freeDSP/FreeDSP_Catamaran_AB/Optinal Balanced Driver Board/Photos/BalancedDriverBoard.jpg

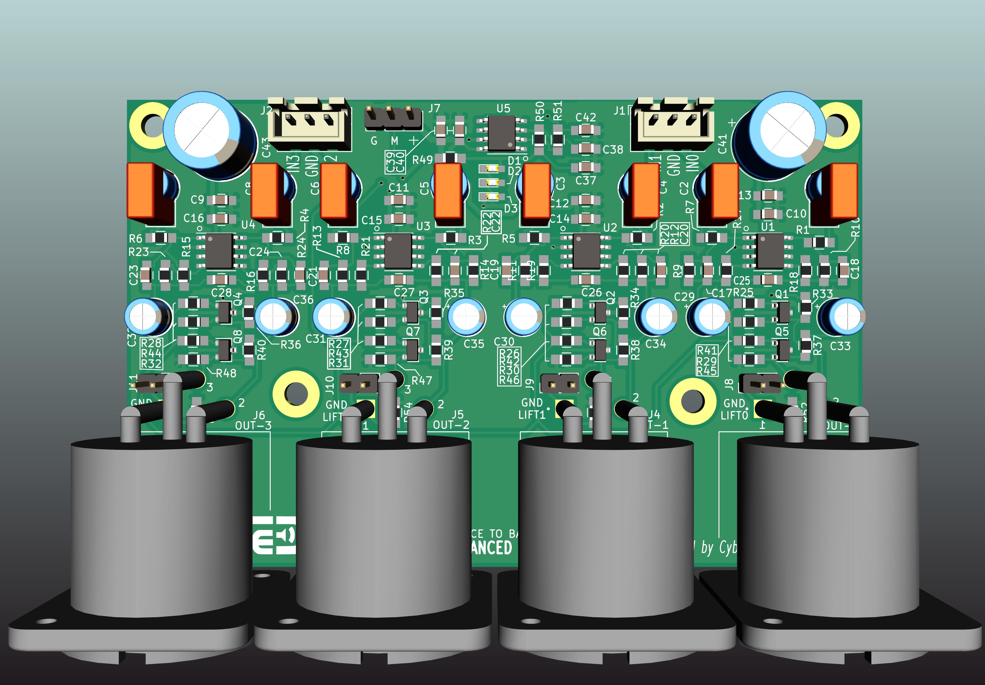
Optinal Balanced Driver Board/Photos/BalancedDriverBoard.jpg
