freeDSP/FreeDSP_Catamaran_AB/Optinal Balanced Driver Board/Photos/BalancedDriverBoard_Bottom.jpg

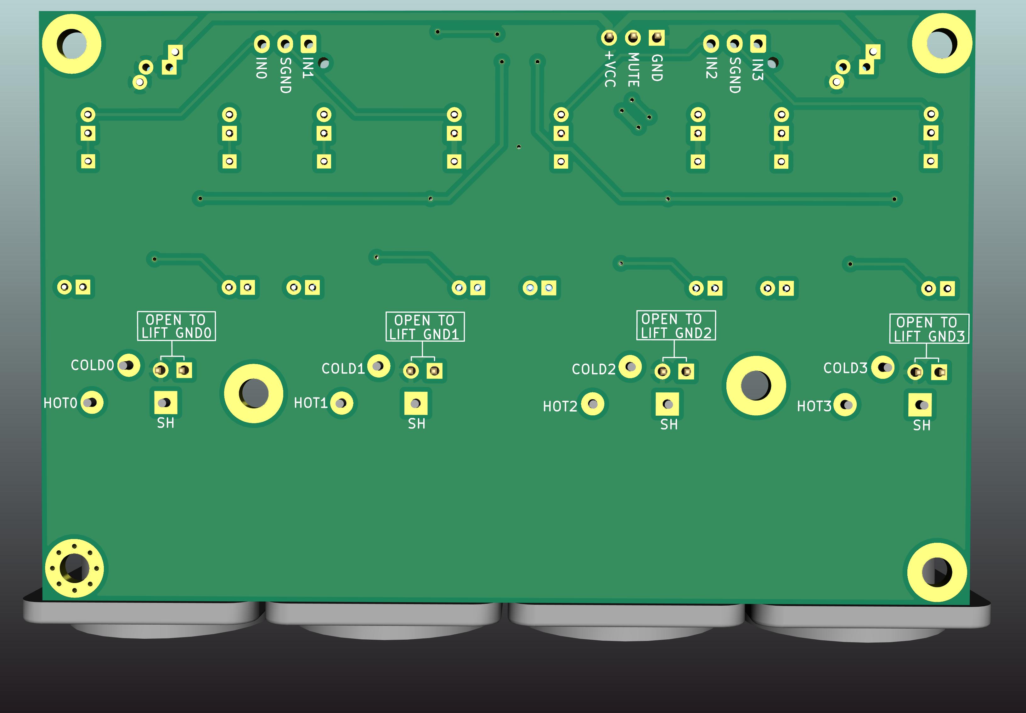
Optinal Balanced Driver Board/Photos/BalancedDriverBoard_Bottom.jpg
