freeDSP/FreeDSP_Catamaran_AB/Optinal Balanced Driver Board/Photos/BalancedDriverBoard_BottomRayTrace.jpg

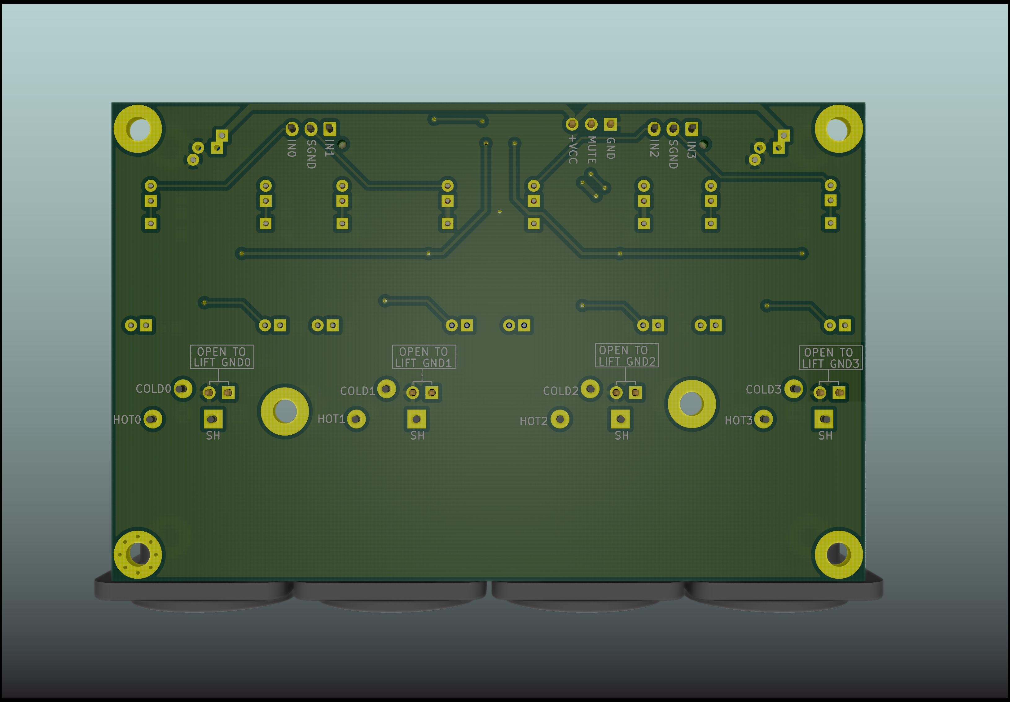
Optinal Balanced Driver Board/Photos/BalancedDriverBoard_BottomRayTrace.jpg
