freeDSP/FreeDSP_Catamaran_AB/Optinal Balanced Driver Board/Photos/BalancedDriverBoard_RayTrace.jpg

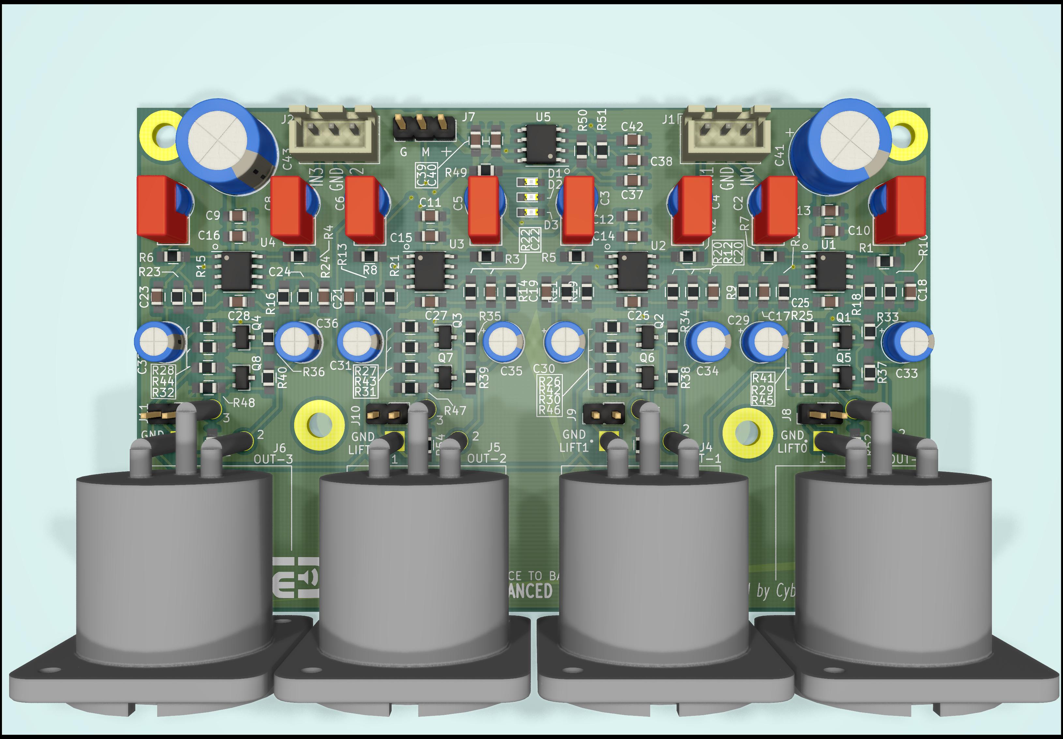
Optinal Balanced Driver Board/Photos/BalancedDriverBoard_RayTrace.jpg
