freeDSP/FreeDSP_Catamaran_AB/Optinal Balanced Driver Board/Photos/BalancedDriverBoardImage.jpg

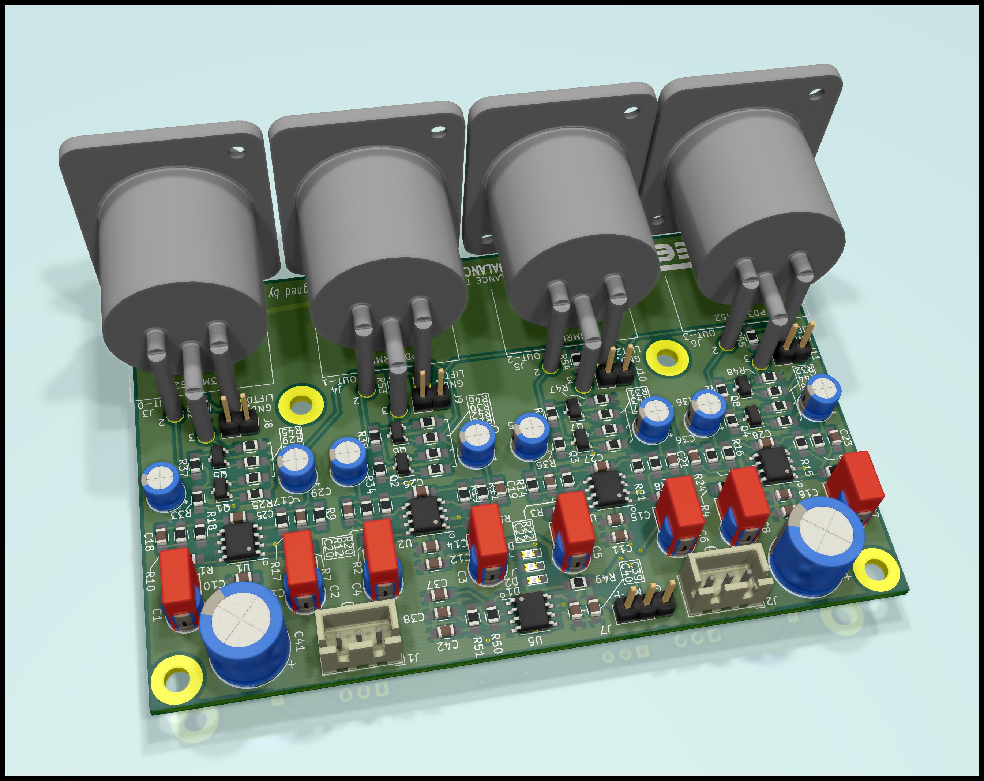
Optinal Balanced Driver Board/Photos/BalancedDriverBoardImage.jpg
