freeDSP/FreeDSP_Catamaran_AB/Photo/0v21PaseView copy.jpg

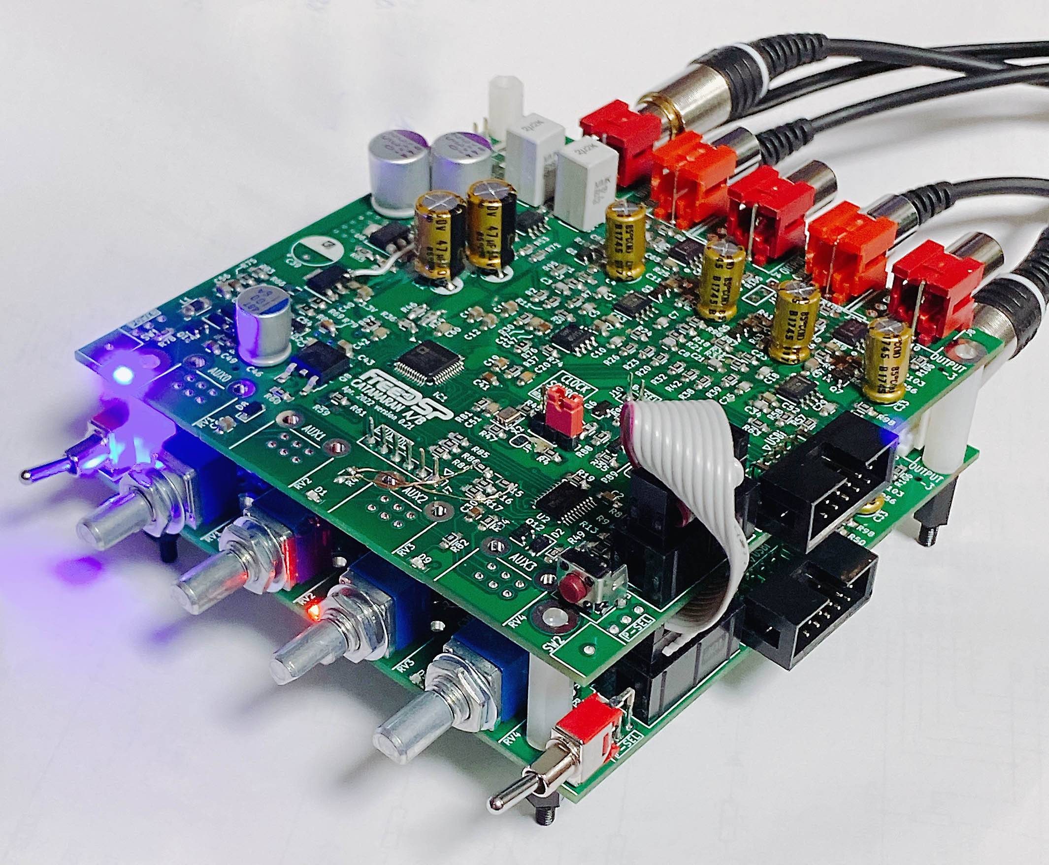
Photo/0v21PaseView copy.jpg
