freeDSP/FreeDSP_Catamaran_AB/Photo/1kHzCrosstalk.png

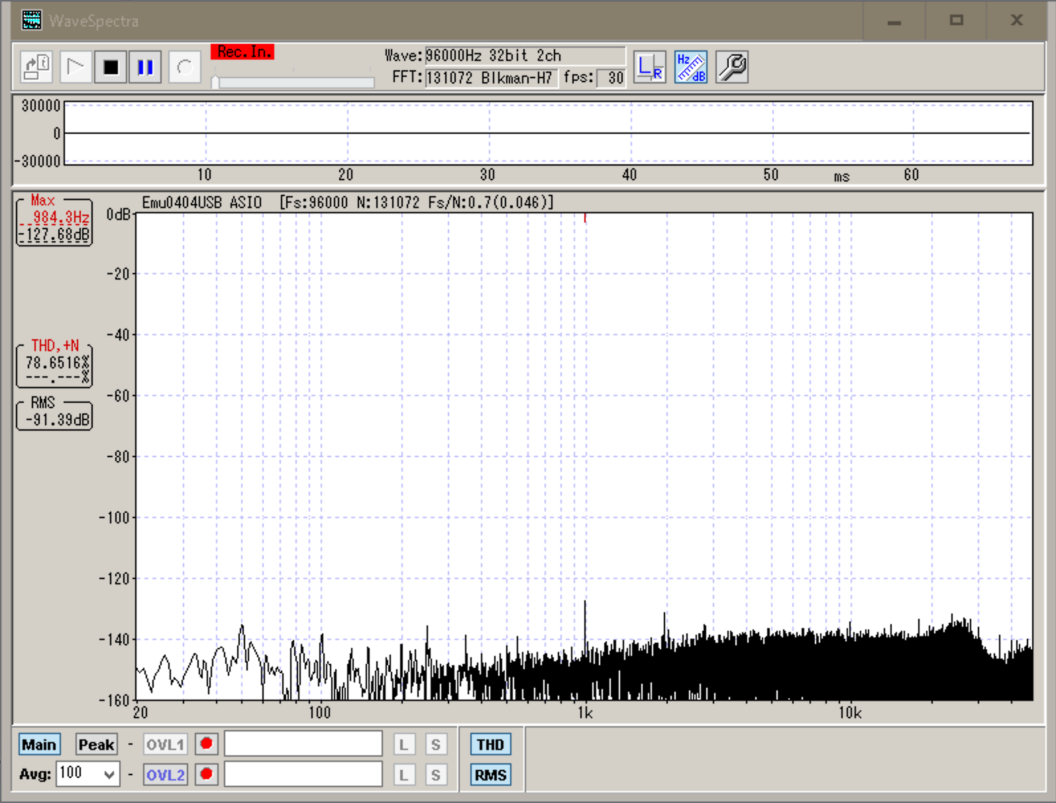
Photo/1kHzCrosstalk.png
