freeDSP/FreeDSP_Catamaran_AB/Photo/4wayCroosover48dBOct.gif

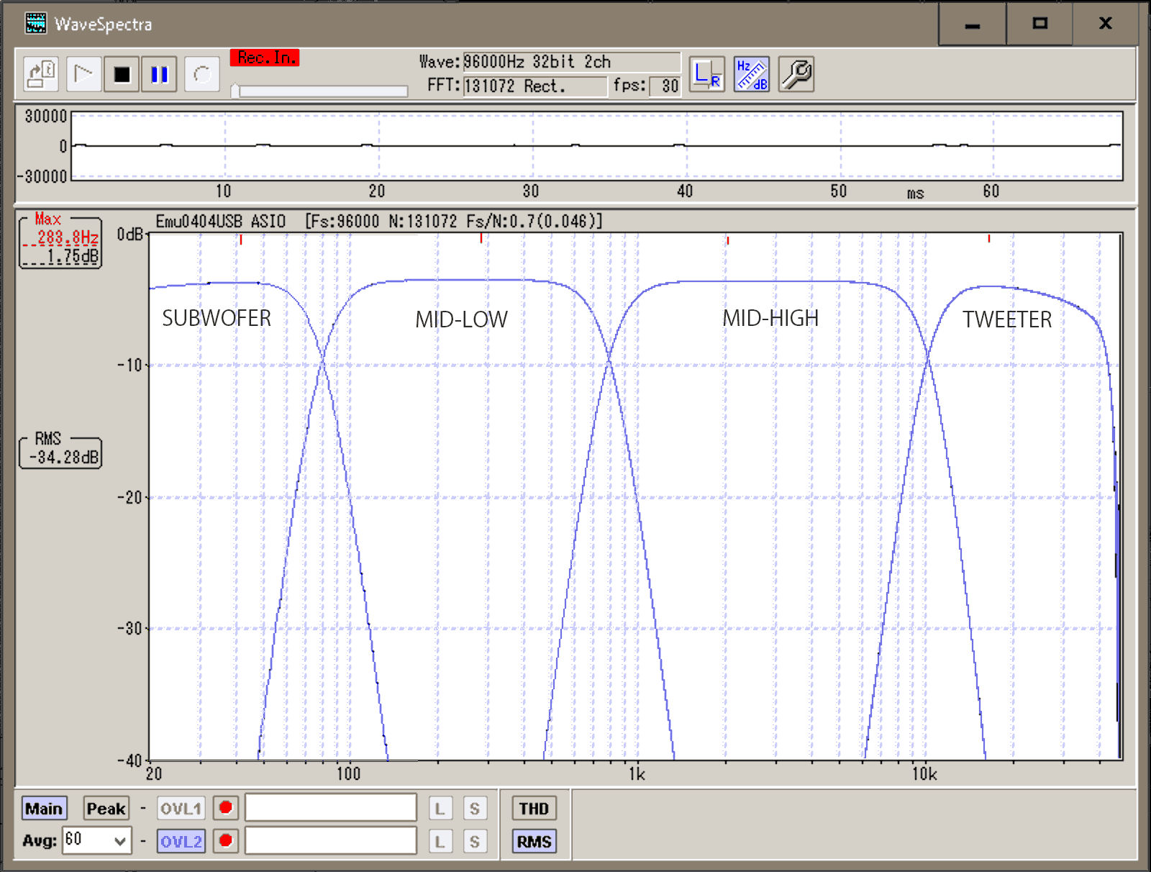
Photo/4wayCroosover48dBOct.gif
