freeDSP/FreeDSP_Catamaran_AB/Photo/FreeDSP_Caramaran_0v21_Master_Photo.JPG

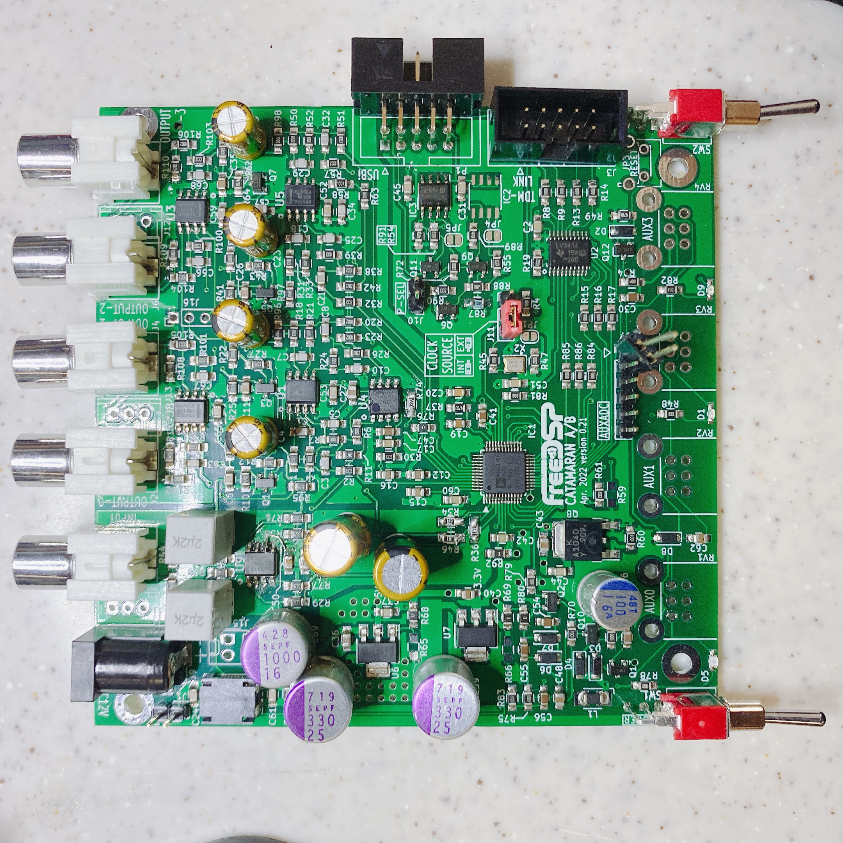
Photo/FreeDSP_Caramaran_0v21_Master_Photo.JPG
