freeDSP/FreeDSP_Catamaran_AB/Photo/FreeDSP_Caramaran_0v21_Slave_Photo.JPG

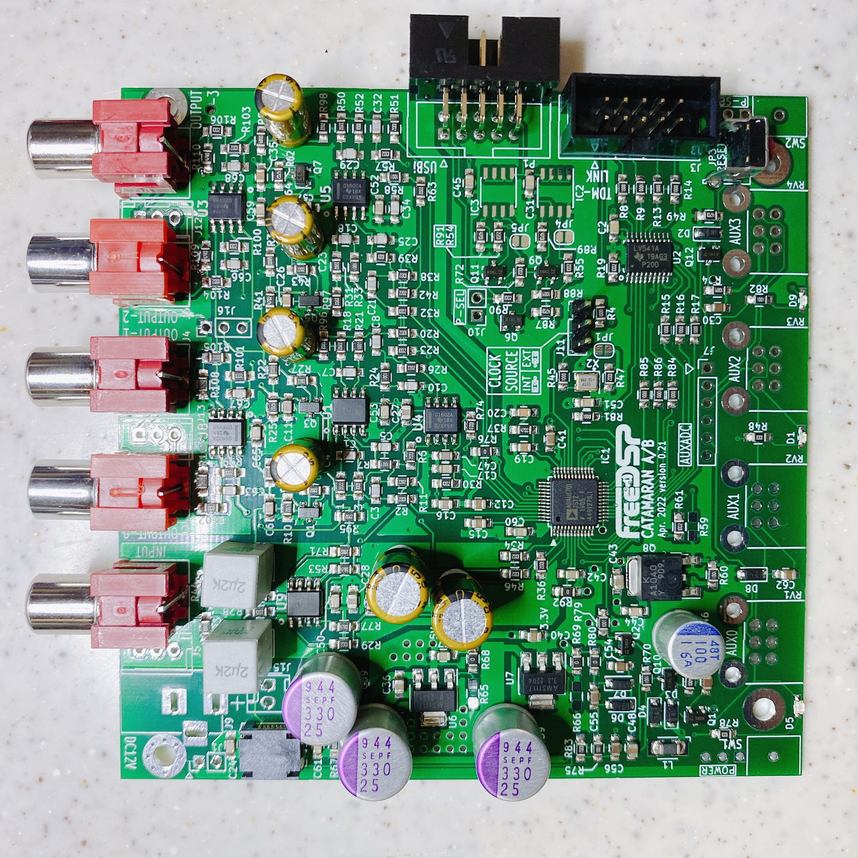
Photo/FreeDSP_Caramaran_0v21_Slave_Photo.JPG
