freeDSP/FreeDSP_Catamaran_AB/Photo/FreeDSP_Catamaran0v2.jpg

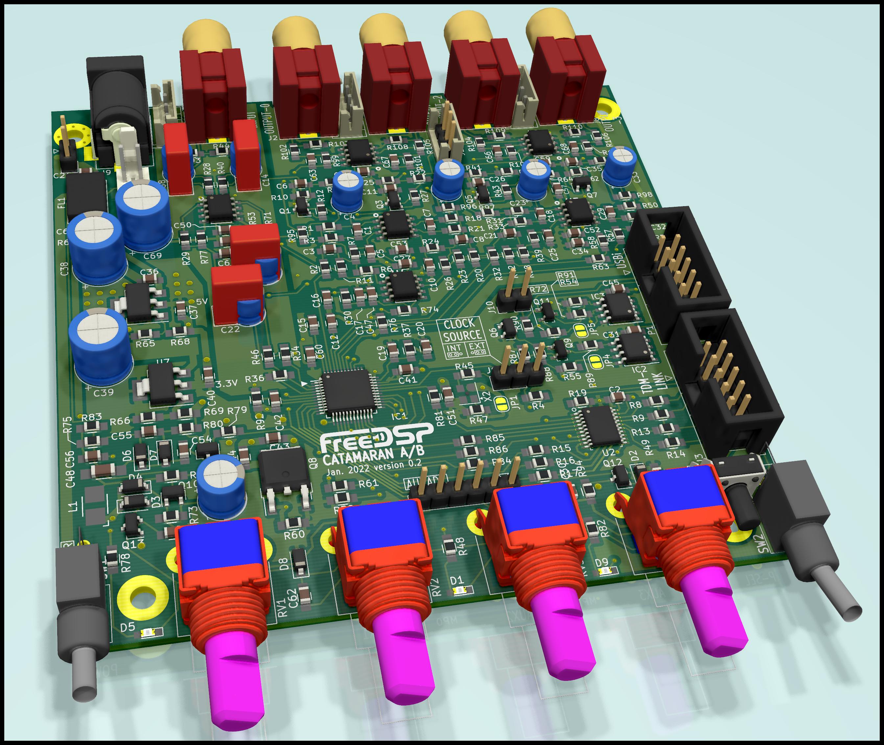
Photo/FreeDSP_Catamaran0v2.jpg
