freeDSP/FreeDSP_Catamaran_AB/Photo/FreeDSP_Catamaran0v2BottomView.jpg

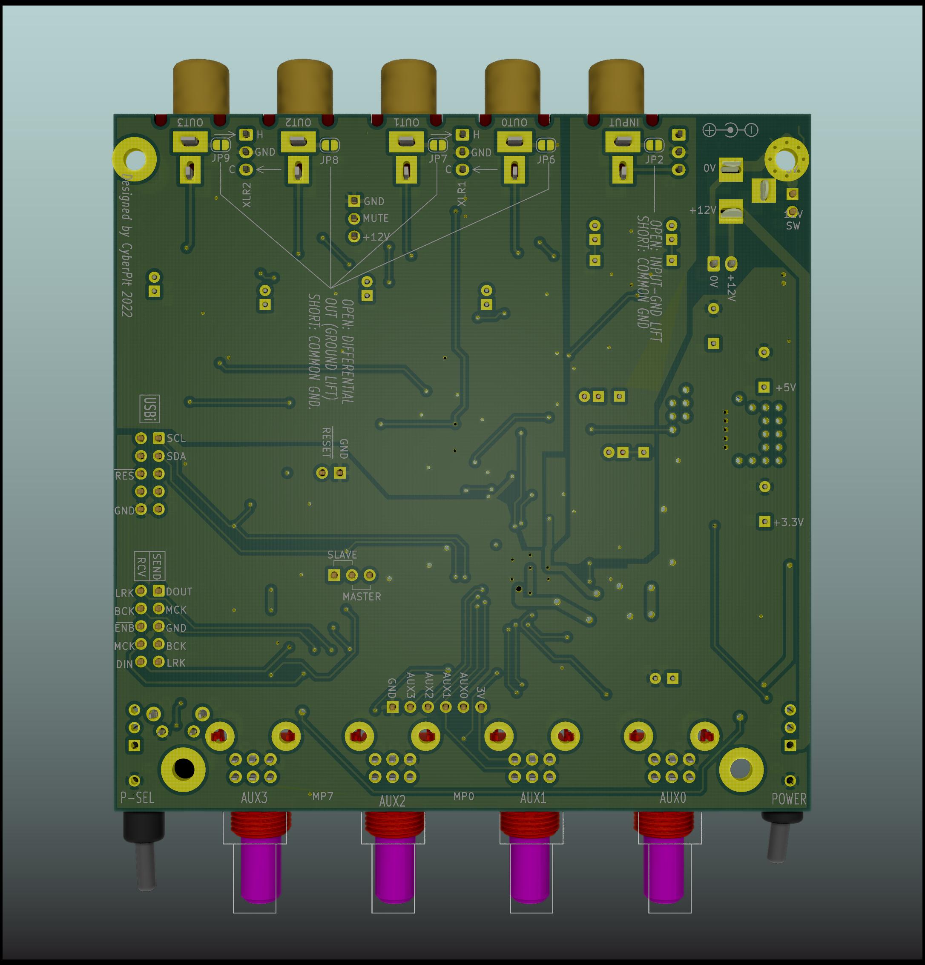
Photo/FreeDSP_Catamaran0v2BottomView.jpg
