freeDSP/FreeDSP_Catamaran_AB/Photo/FreeDSP_Catamaran0v2TopView.jpg

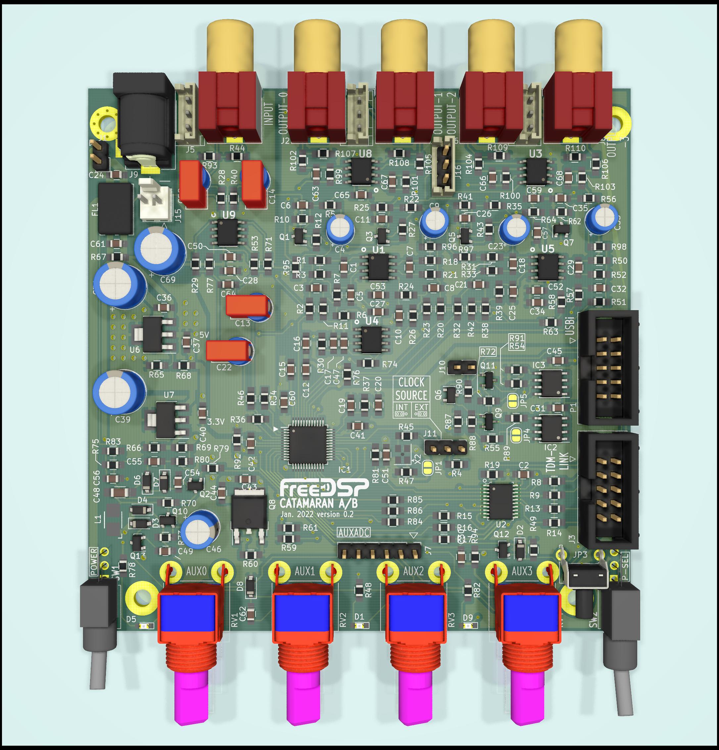
Photo/FreeDSP_Catamaran0v2TopView.jpg
