freeDSP/FreeDSP_Catamaran_AB/Photo/FreeDSP_Catamaran_1v0_TopRender.jpg

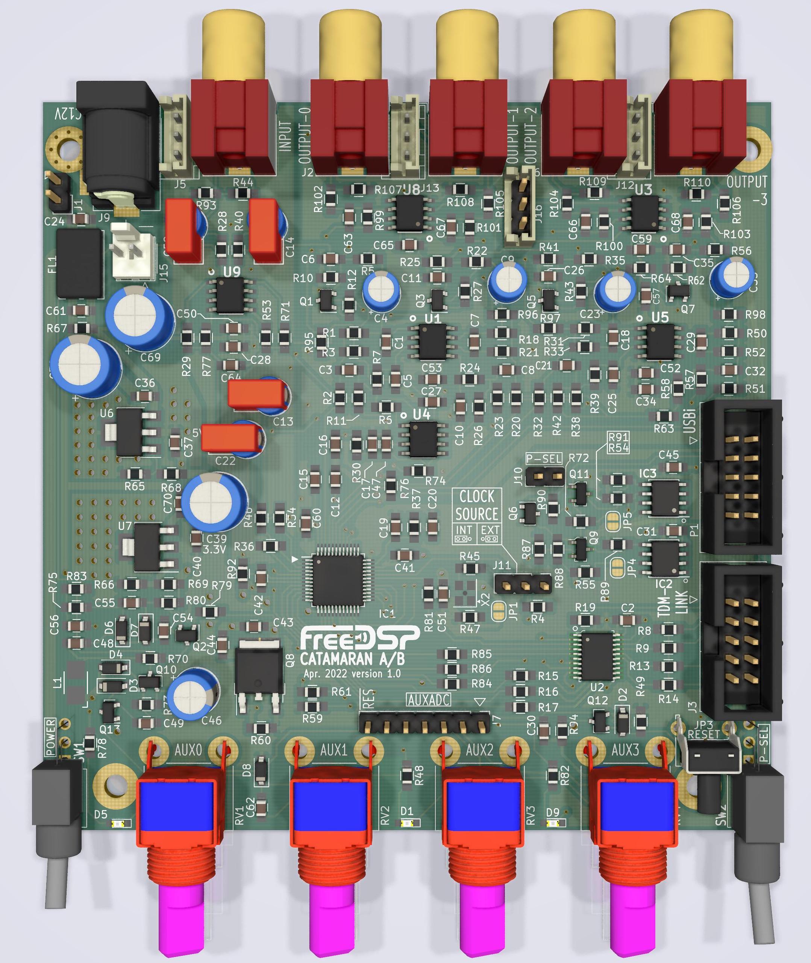
Photo/FreeDSP_Catamaran_1v0_TopRender.jpg
