freeDSP/FreeDSP_Catamaran_AB/Photo/FreeDSP_Catamaran_1v2_TopRendering.jpg

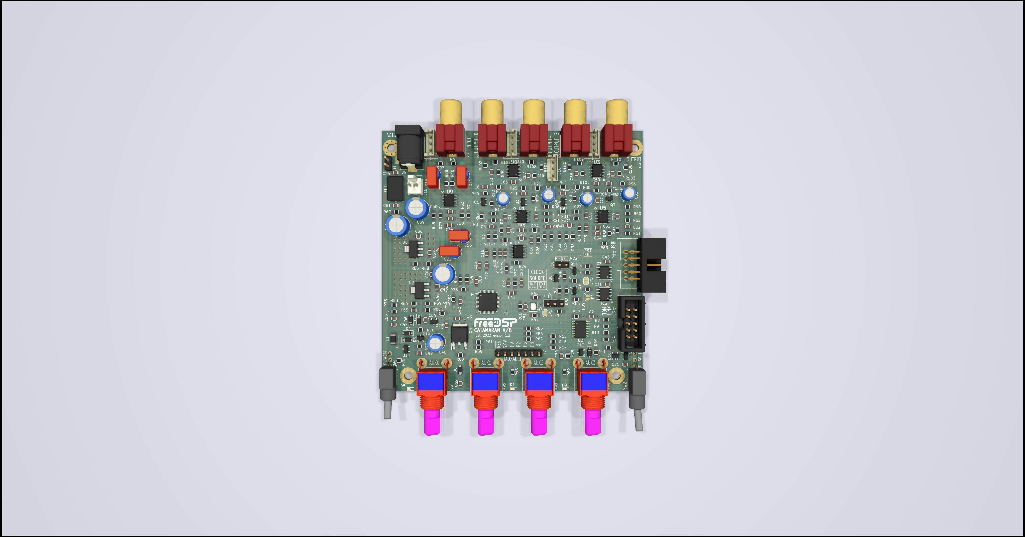
Photo/FreeDSP_Catamaran_1v2_TopRendering.jpg
