freeDSP/FreeDSP_Catamaran_AB/Photo/FreeDSP_Catamaran_SinWave96kHzOverallDistortion.png

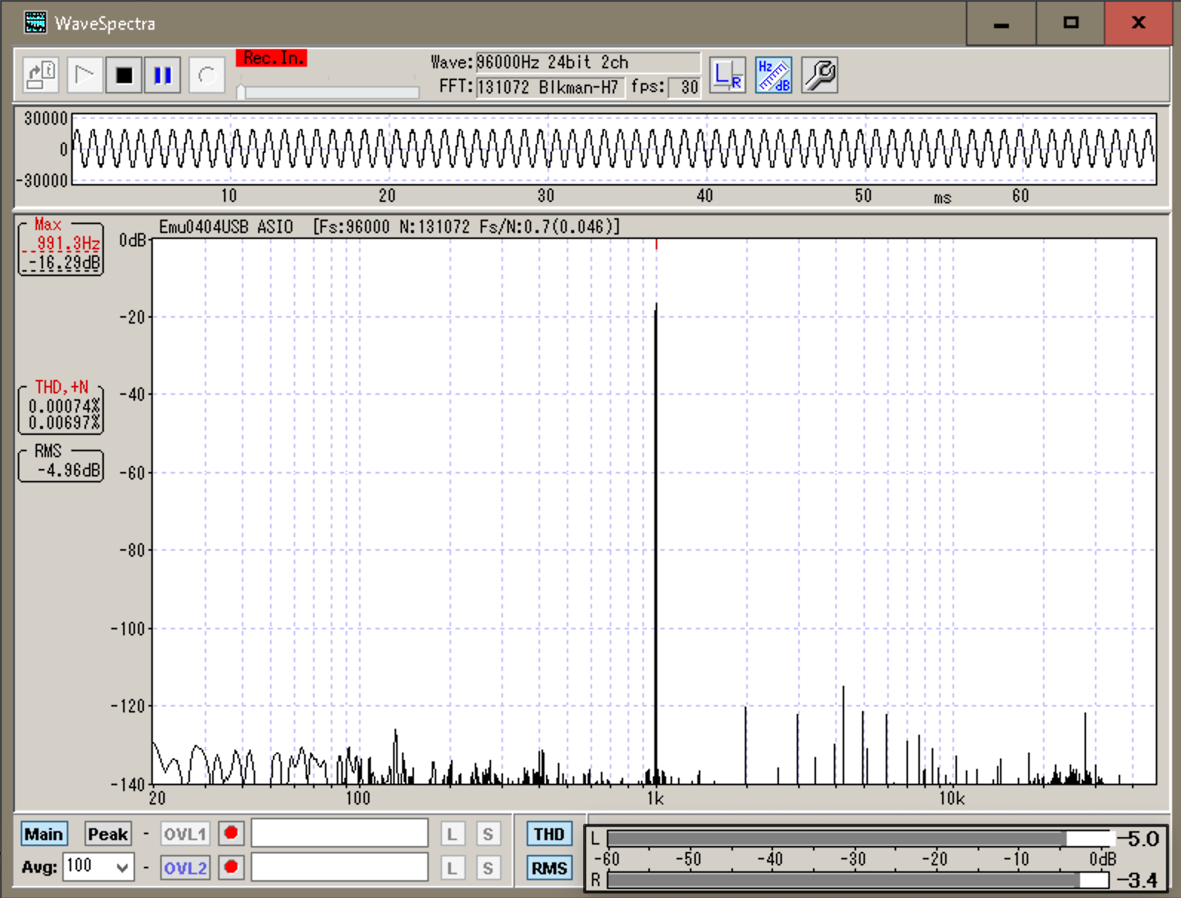
Photo/FreeDSP_Catamaran_SinWave96kHzOverallDistortion.png
