freeDSP/FreeDSP_Catamaran_AB/Photo/IMG_5258.JPG

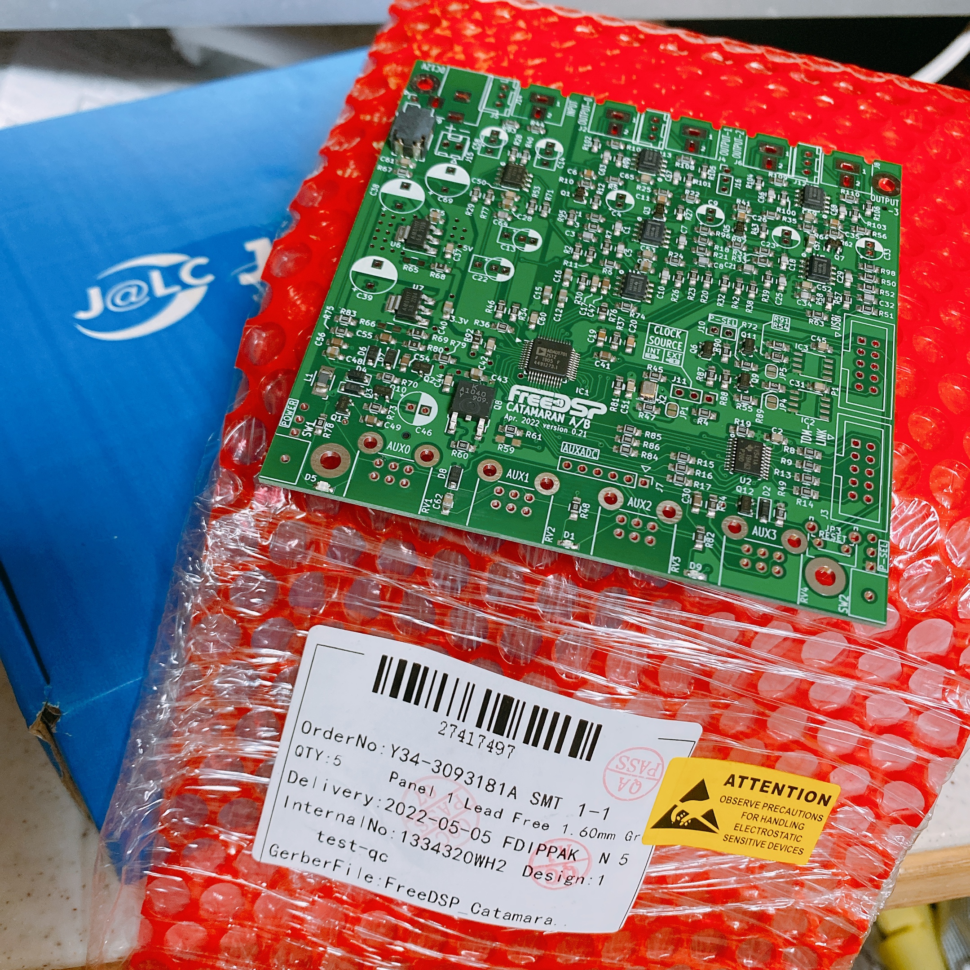
Photo/IMG_5258.JPG
