freeDSP/FreeDSP_Catamaran_AB/Photo/MainBoard_Bottom.JPG

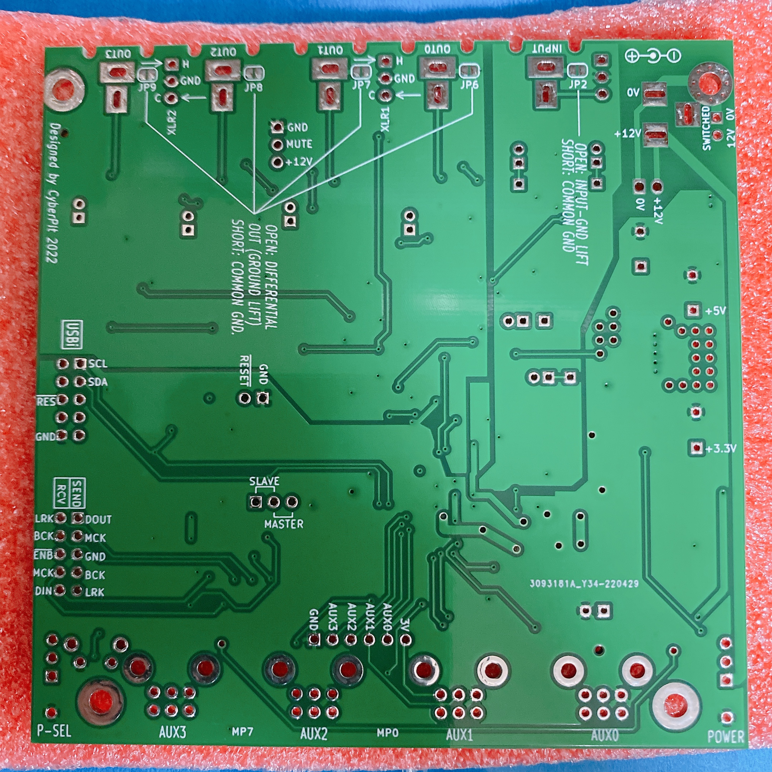
Photo/MainBoard_Bottom.JPG
