freeDSP/FreeDSP_Catamaran_AB/Photo/MainBoard_Top-SMT.JPG

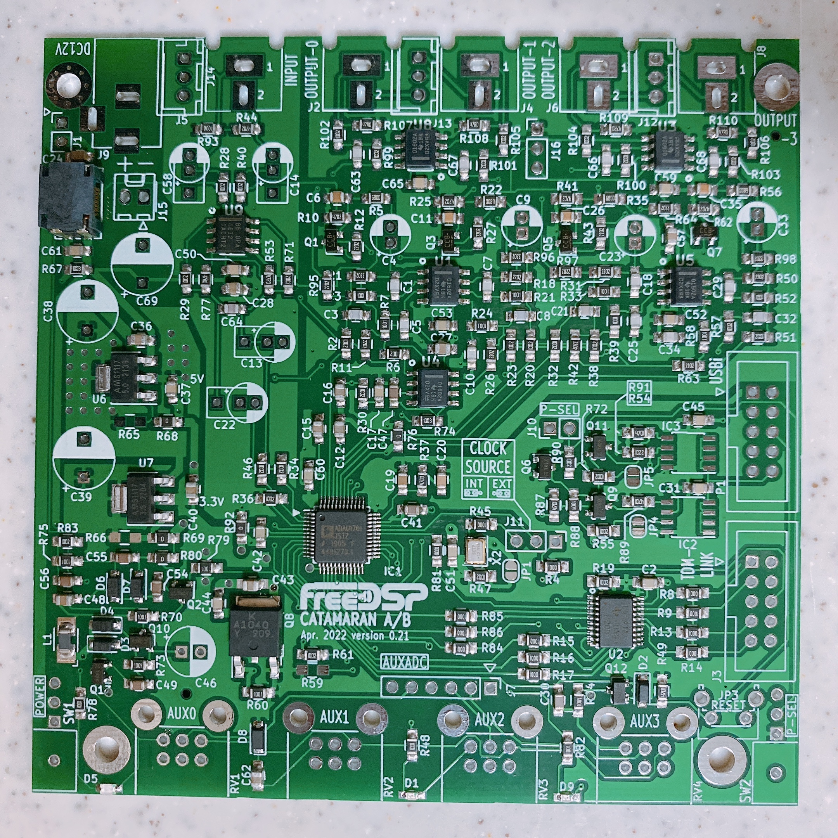
Photo/MainBoard_Top-SMT.JPG
