freeDSP/FreeDSP_Catamaran_AB/Photo/TDM-LINK_Cable.jpg

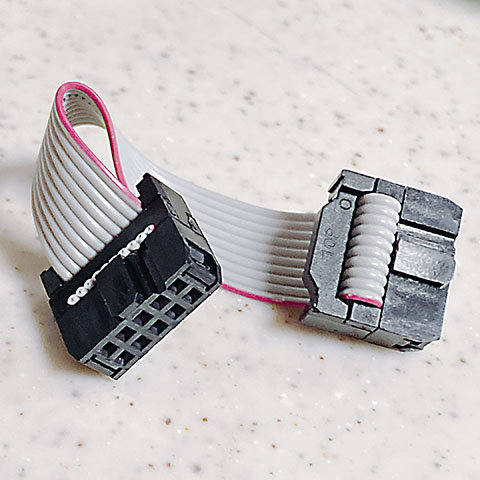
Photo/TDM-LINK_Cable.jpg
