freeDSP/FreeDSP_Catamaran_AB/Photo/4way_24dBOct_CD_Master_373steps.png

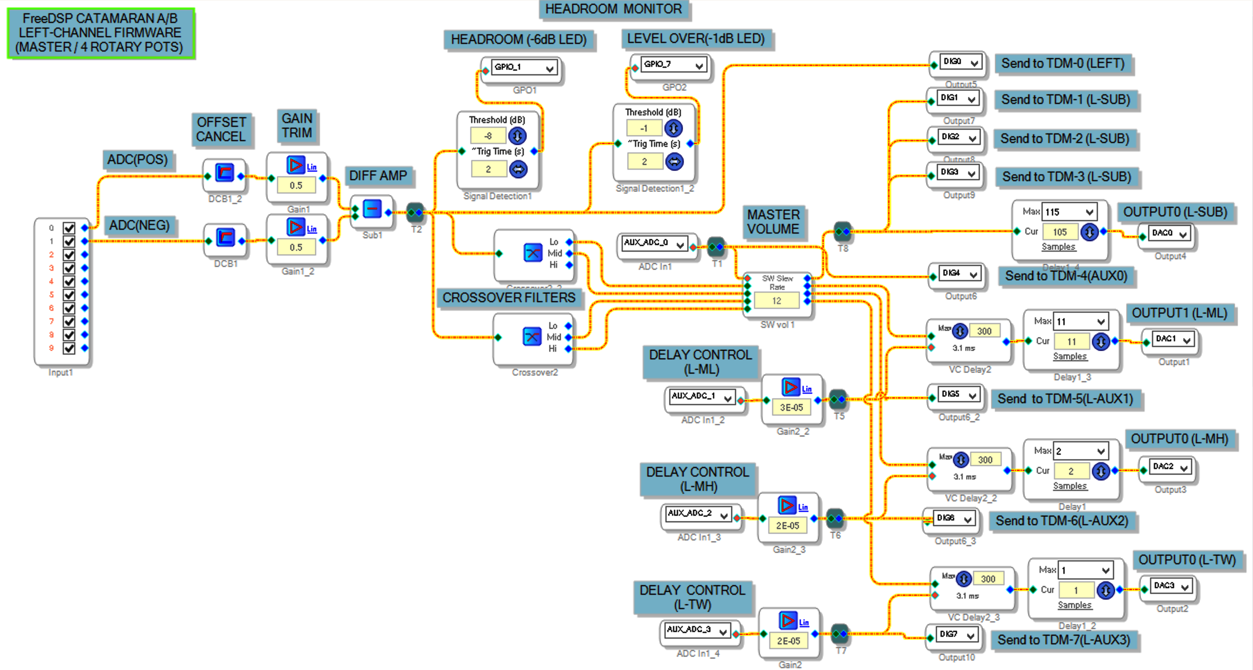
Photo/4way_24dBOct_CD_Master_373steps.png
