freeDSP/FreeDSP_Catamaran_AB/Photo/4way_24dBOct_CD_Slave_356steps.png

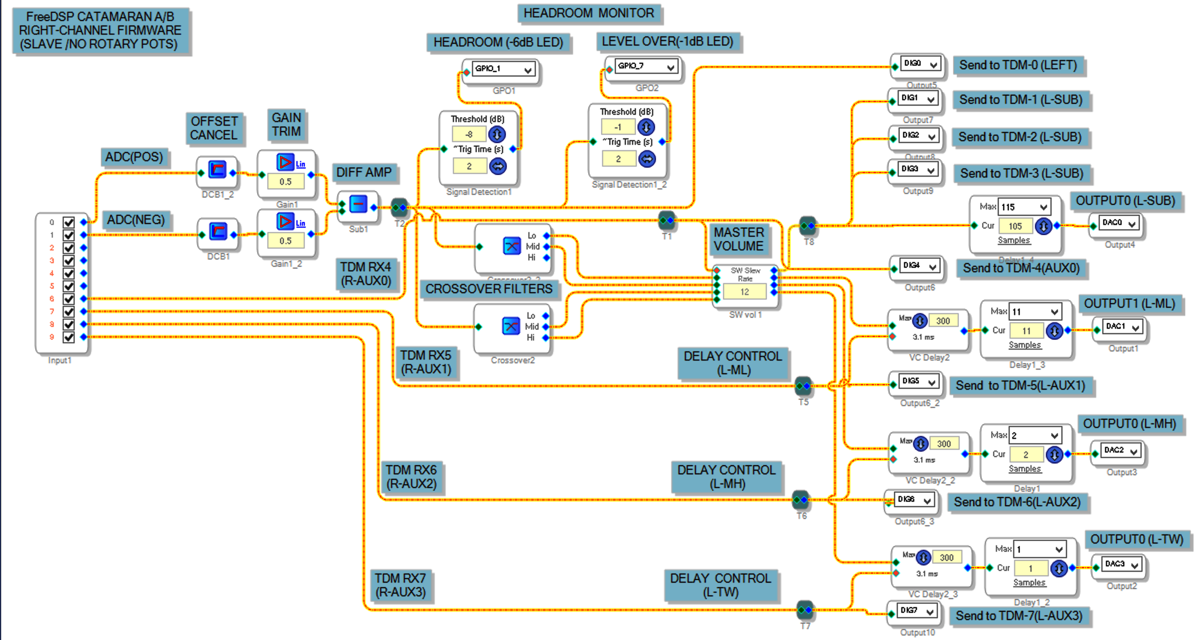
Photo/4way_24dBOct_CD_Slave_356steps.png
